STEL-Pitt-BioE/HemoLens/Assembly/RAMP/RAMP_Build_Plate.3mf

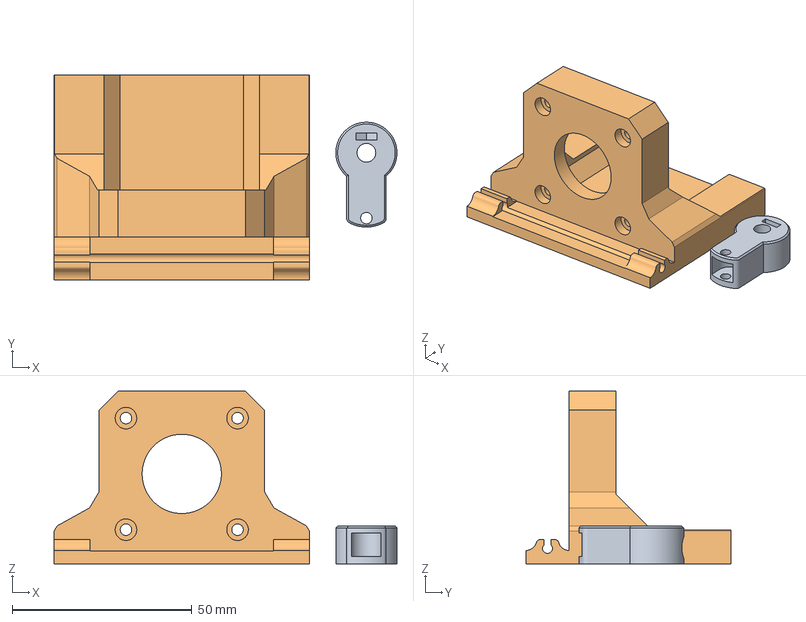
[picture p16: CAD file, 2025-04-23]
Assembly/RAMP/RAMP_Build_Plate.3mf
95.3 x 57.0 x 48.0 mm
RAMP_Gate.step
RAMP_Main.step
