STEL-Pitt-BioE/HemoLens/Assembly/Camera Gantry/STEP Files/Camera_Bracket.step

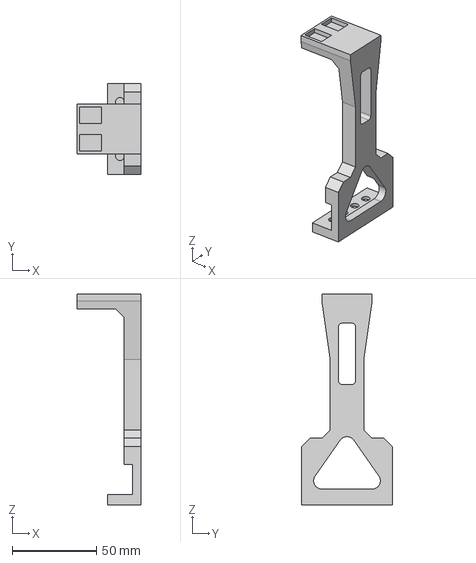
[picture p17: CAD file, 2025-01-18]
Assembly/Camera Gantry/STEP Files/Camera_Bracket.step
38.0 x 53.8 x 125.4 mm
