STEL-Pitt-BioE/HemoLens/Assembly/Main Platform/Cradle_Plate.3mf

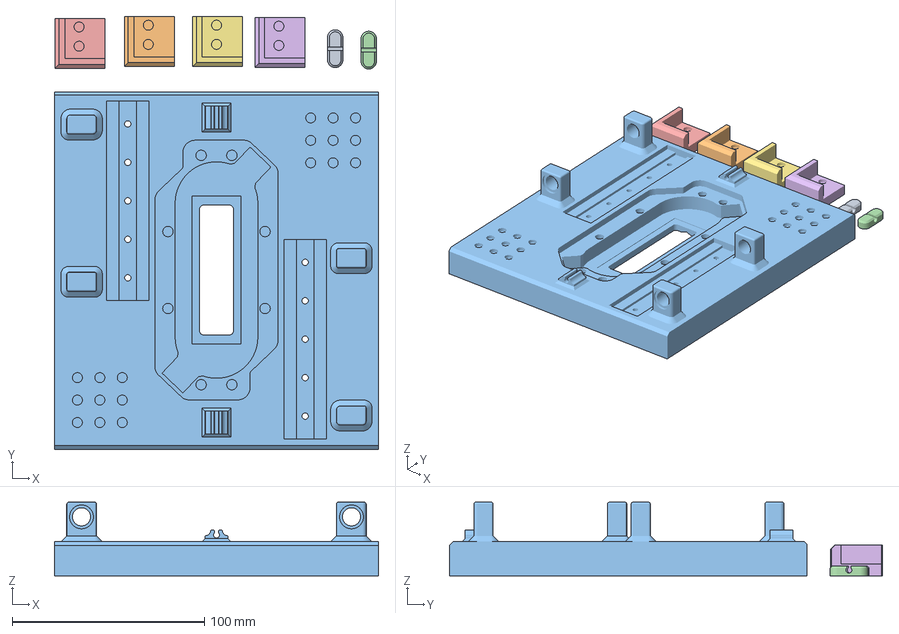
[picture p18: CAD file, 2025-04-23]
Assembly/Main Platform/Cradle_Plate.3mf
168.6 x 225.1 x 38.3 mm
Tubing_Holder.step x 2
Cradle_Feet.stl x 4
Cradle.step
