STEL-Pitt-BioE/HemoLens/Assembly/Main Platform/STEP Files/Cradle.step

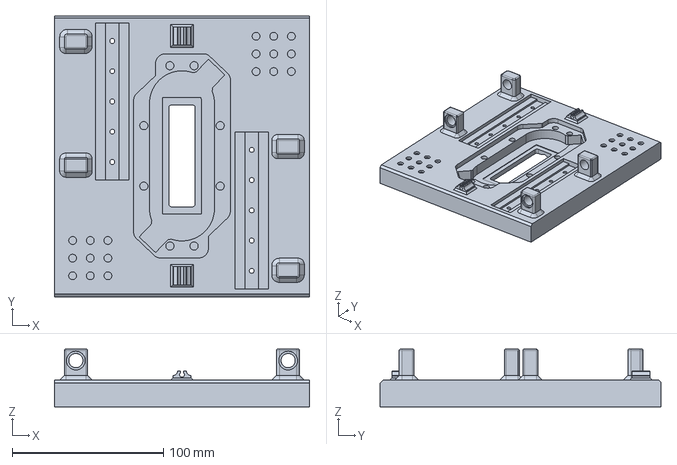
[picture p19: CAD file, 2025-01-19]
Assembly/Main Platform/STEP Files/Cradle.step
168.6 x 185.8 x 38.3 mm
