STEL-Pitt-BioE/HemoLens/Assembly/Micromanipulators/STEP Files/Z_Axis_Accessory.step

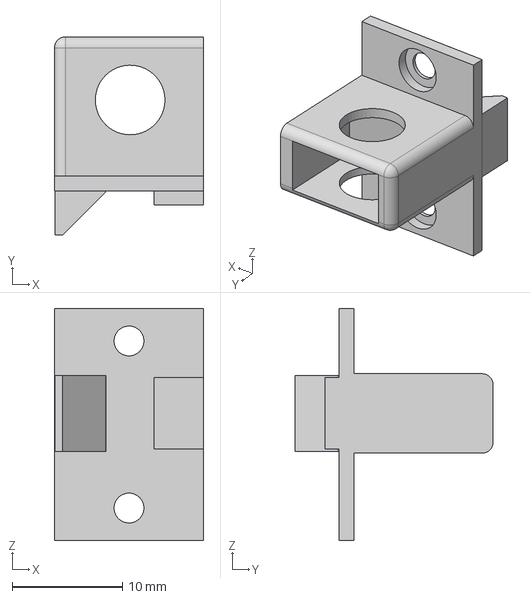
[picture p20: CAD file, 2025-01-18]
Assembly/Micromanipulators/STEP Files/Z_Axis_Accessory.step
13.5 x 18.0 x 21.0 mm
