STEL-Pitt-BioE/HemoLens/Assembly/Pressure Crank/STEP Files/iRPS_Syringe_Holder.step

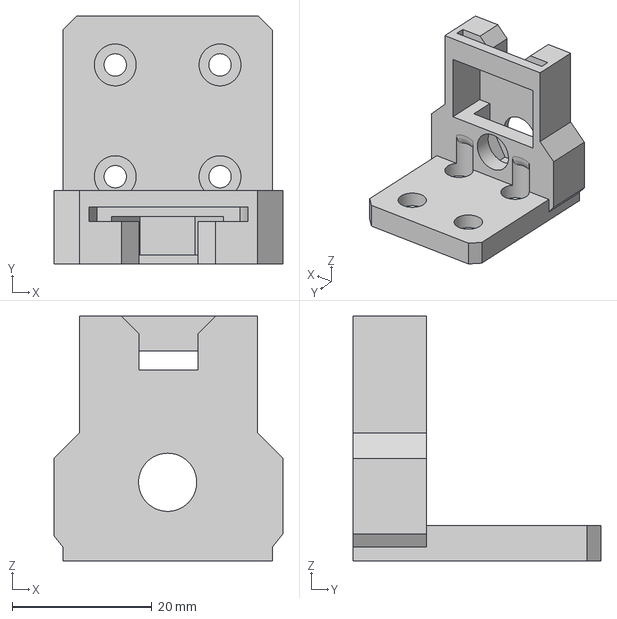
[picture p21: CAD file, 2025-01-18]
Assembly/Pressure Crank/STEP Files/iRPS_Syringe_Holder.step
32.8 x 35.5 x 35.1 mm
