STEL-Pitt-BioE/HemoLens/Assembly/RAMP/STEP Files/RAMP 80-145+ mmHg Adapter.step

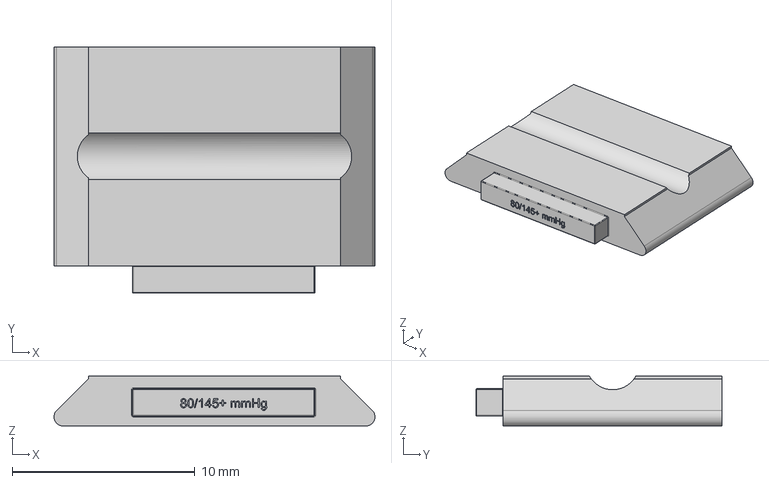
[picture p22: CAD file, 2025-01-18]
Assembly/RAMP/STEP Files/RAMP 80-145+ mmHg Adapter.step
17.6 x 13.5 x 2.74 mm
