STEL-Pitt-BioE/HemoLens/Assembly/Camera Gantry/STEP Files/Camera_Z_Stage.step

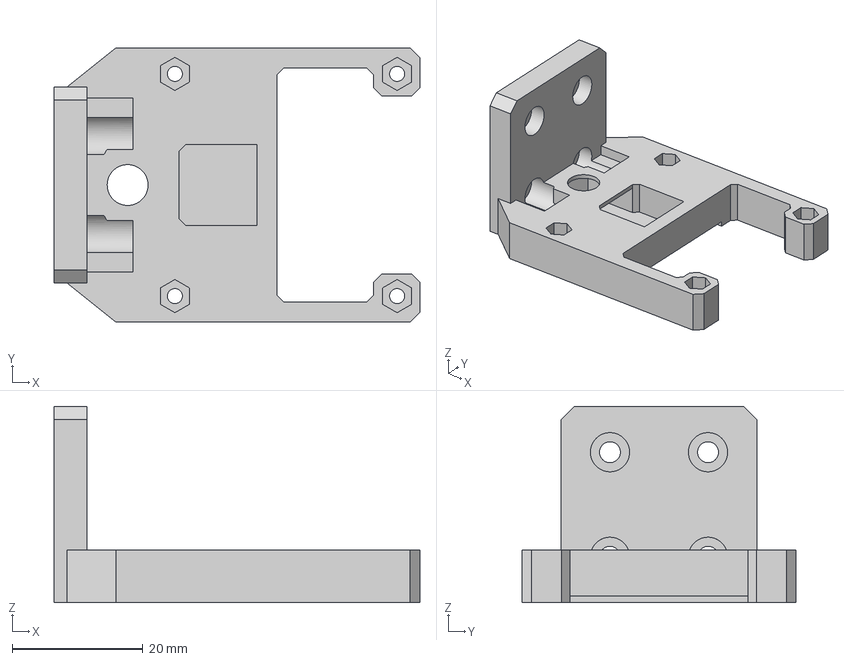
[picture p23: CAD file, 2025-01-18]
Assembly/Camera Gantry/STEP Files/Camera_Z_Stage.step
56.0 x 42.0 x 30.0 mm
