STEL-Pitt-BioE/HemoLens/Assembly/Main Platform/STEP Files/Tubing_Holder.step

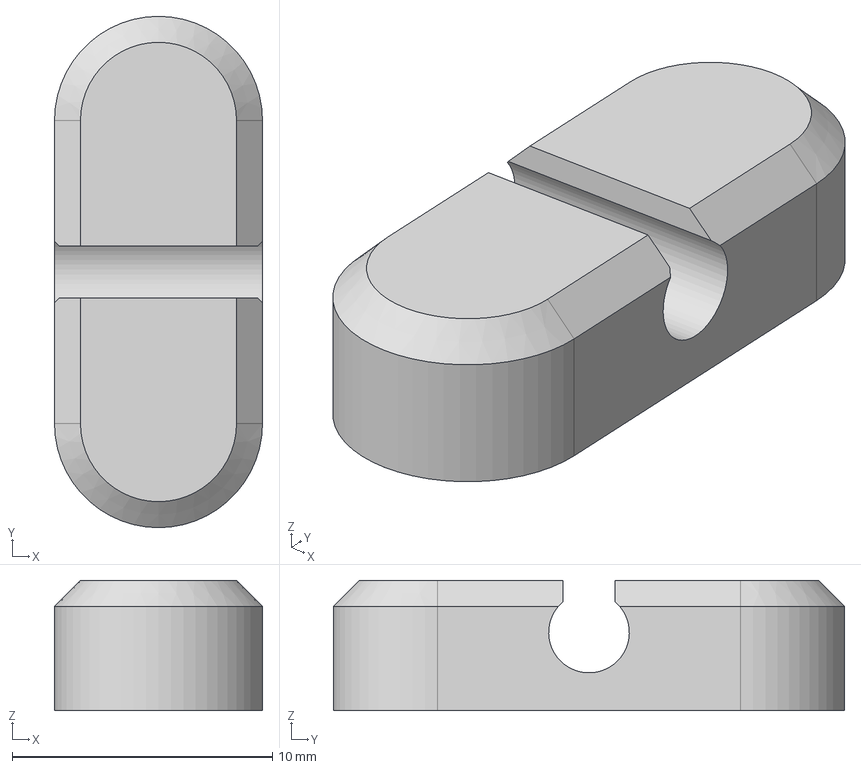
[picture p24: CAD file, 2025-01-19]
Assembly/Main Platform/STEP Files/Tubing_Holder.step
8.00 x 19.7 x 5.00 mm
