STEL-Pitt-BioE/HemoLens/Assembly/RAMP/STEP Files/RAMP_Gate.step

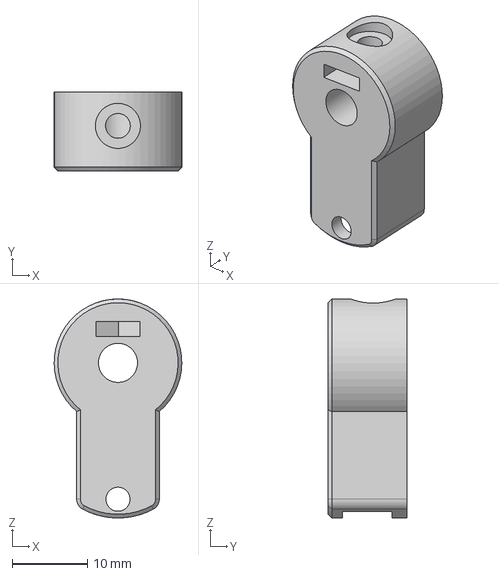
[picture p25: CAD file, 2025-01-18]
Assembly/RAMP/STEP Files/RAMP_Gate.step
17.0 x 10.5 x 29.1 mm
