STEL-Pitt-BioE/HemoLens/Assembly/Main Platform/STEP Files/Cradle_Feet.step

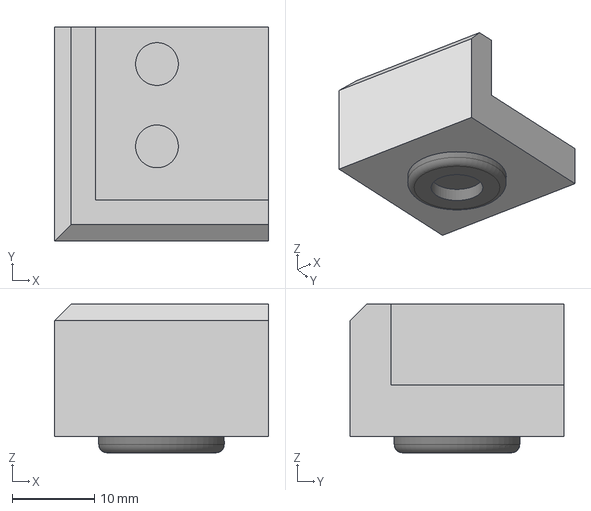
[picture p26: CAD file, 2025-01-19]
Assembly/Main Platform/STEP Files/Cradle_Feet.step
26.0 x 26.0 x 18.0 mm
