STEL-Pitt-BioE/HemoLens/Assembly/Micromanipulators/STEP Files/Cannula_Sub.step

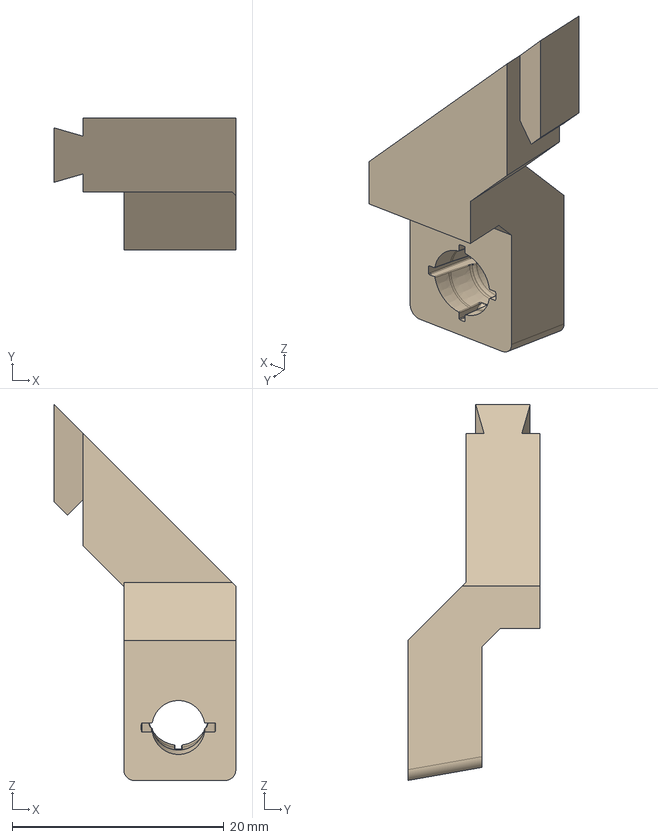
[picture p27: CAD file, 2025-01-18]
Assembly/Micromanipulators/STEP Files/Cannula_Sub.step
17.1 x 12.5 x 35.5 mm
