STEL-Pitt-BioE/HemoLens/Assembly/Micromanipulators/STEP Files/Manipulator_Y_Axis.step

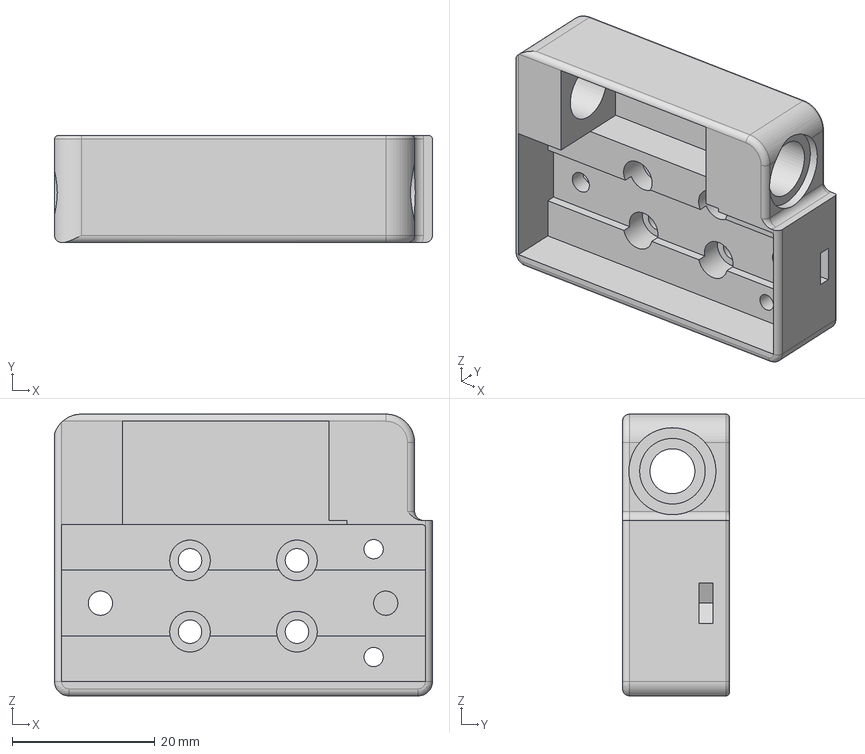
[picture p29: CAD file, 2025-01-18]
Assembly/Micromanipulators/STEP Files/Manipulator_Y_Axis.step
53.0 x 15.0 x 39.5 mm
